husky-koglhof/CPRD/data/cycle.png

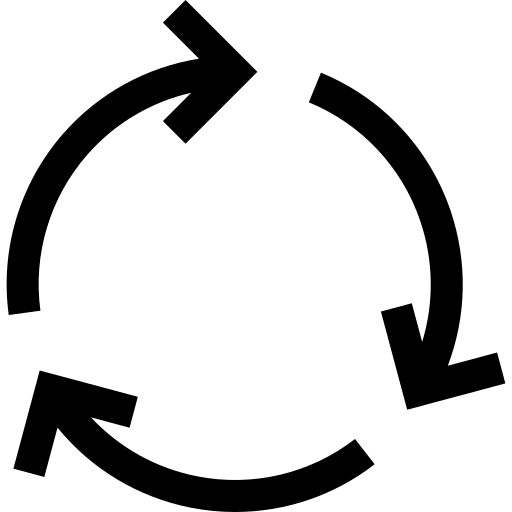
data/cycle.png
