husky-koglhof/CPRD/data/thermometer.png

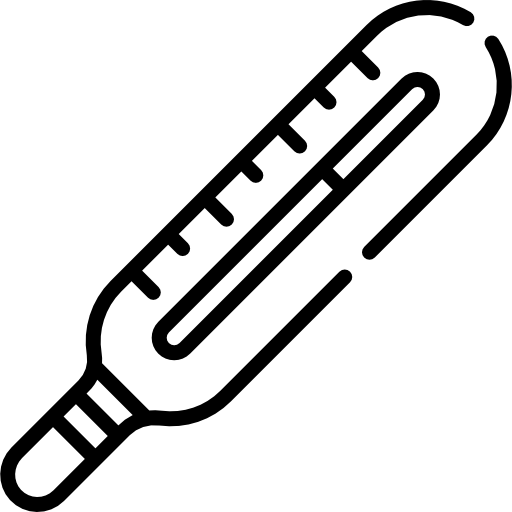
data/thermometer.png
