husky-koglhof/CPRD/fritzing/Puppe5_pcb.png

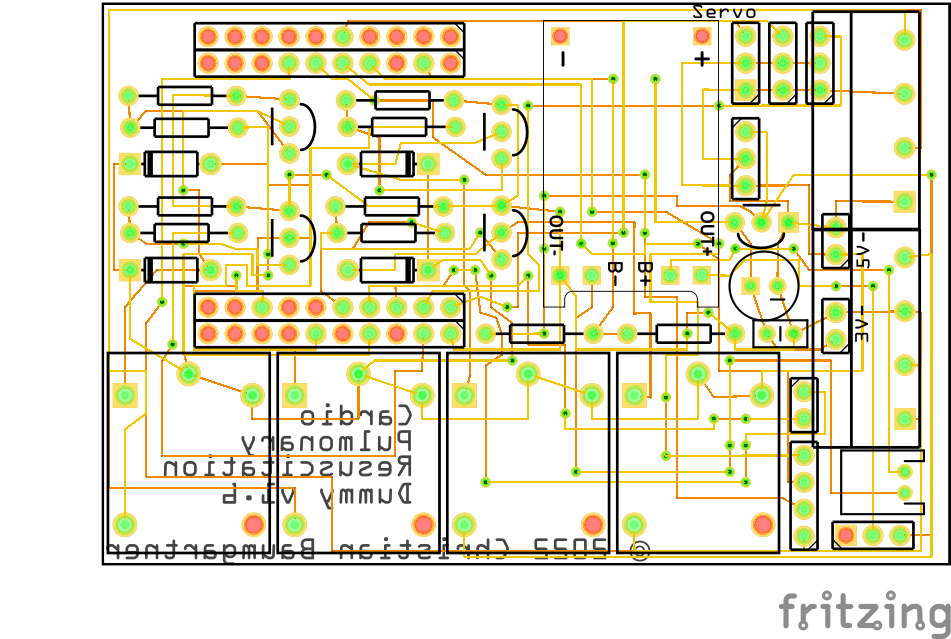
fritzing/Puppe5_pcb.png
